rcalme/puzzle-box/Drawers/Center/center_drawer.pdf

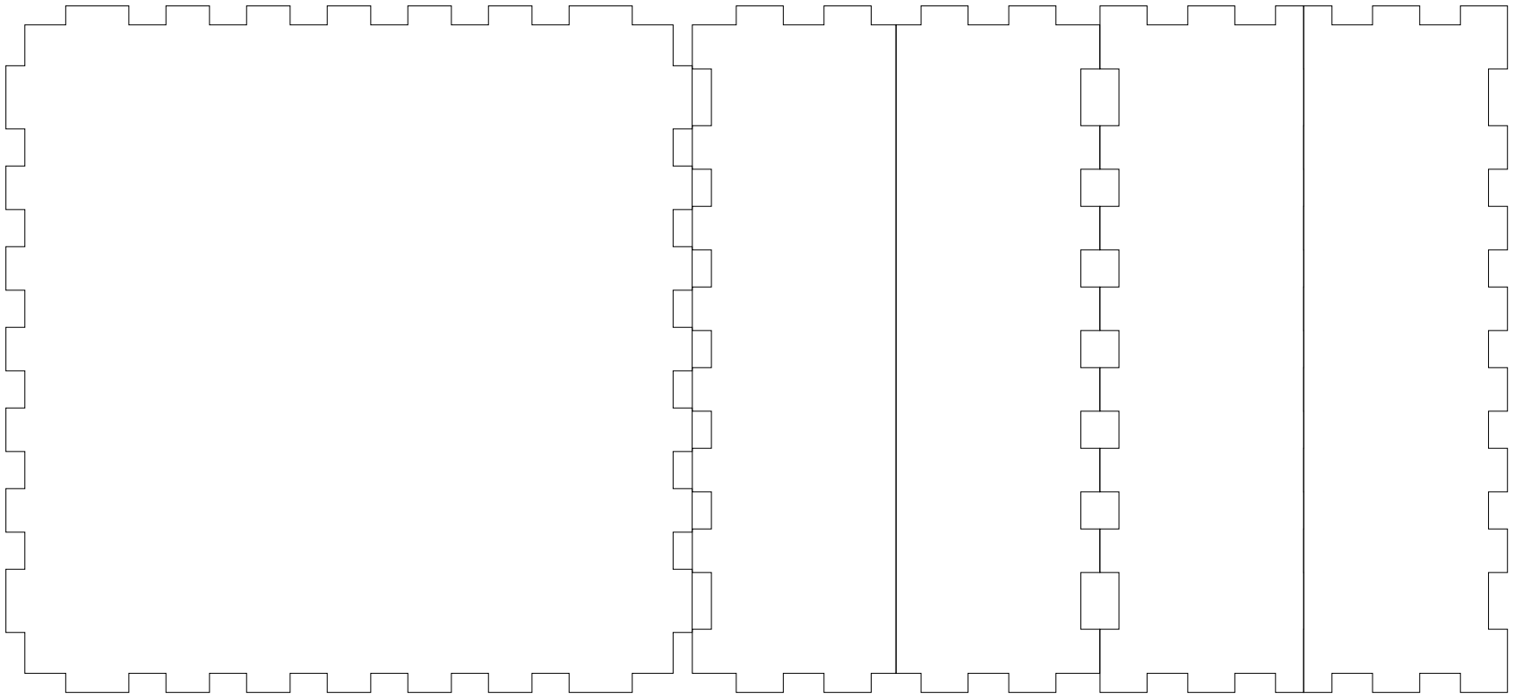
[picture p23: figure]
