rcalme/puzzle-box/Drawers/Left/left_drawer.pdf

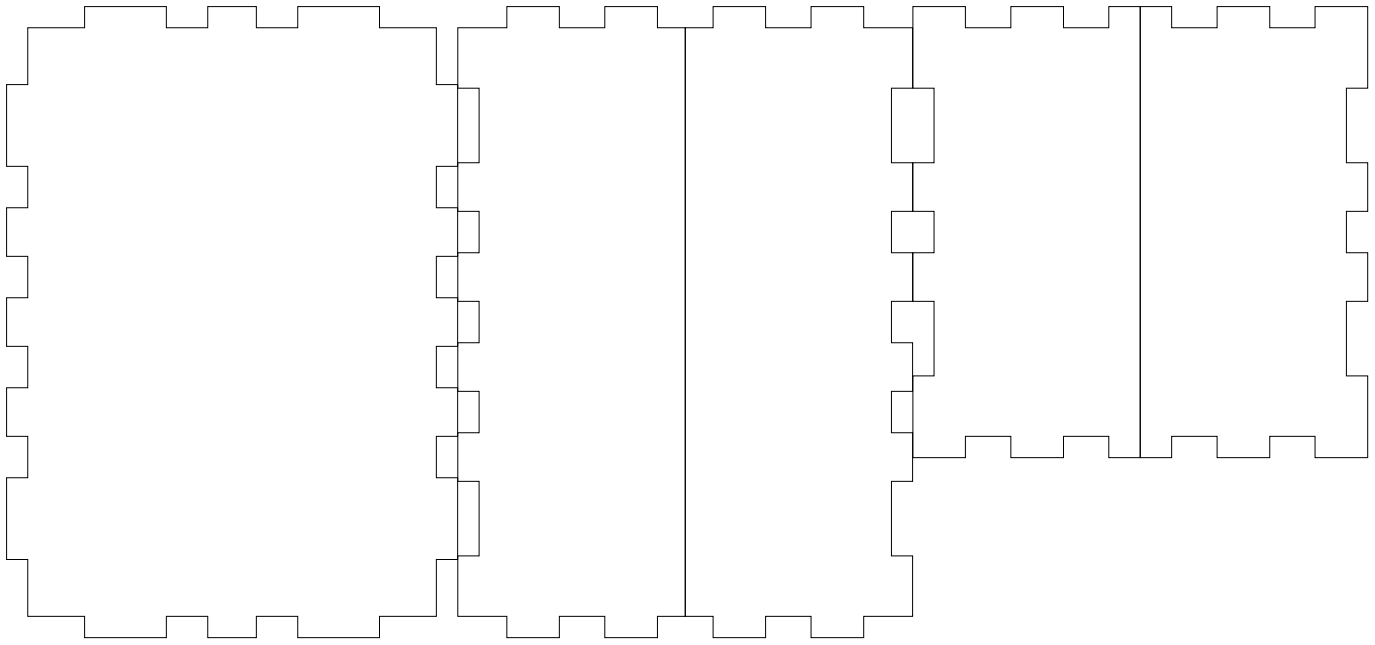
[picture p24: figure]
