rcalme/puzzle-box/All_In_One/Laser/Key_Slider/key_slider_0125_acrylic.png

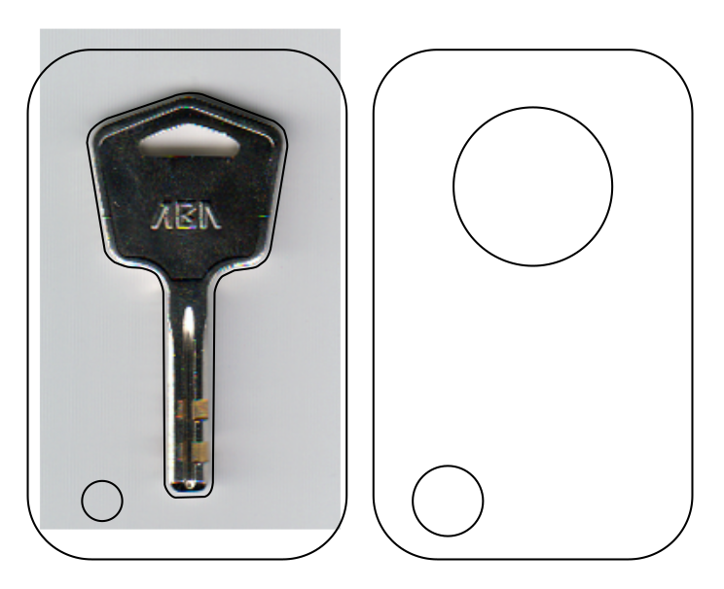
All_In_One/Laser/Key_Slider/key_slider_0125_acrylic.png
