rcalme/puzzle-box/Drawers/Key/key.png

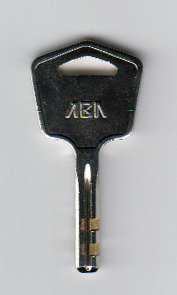
Drawers/Key/key.png
