rcalme/puzzle-box/Magnet_Grid/Clue/clue.png

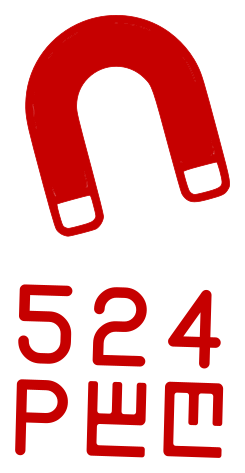
Magnet_Grid/Clue/clue.png
