rcalme/puzzle-box/Process/Images/01_Generating_gears.png

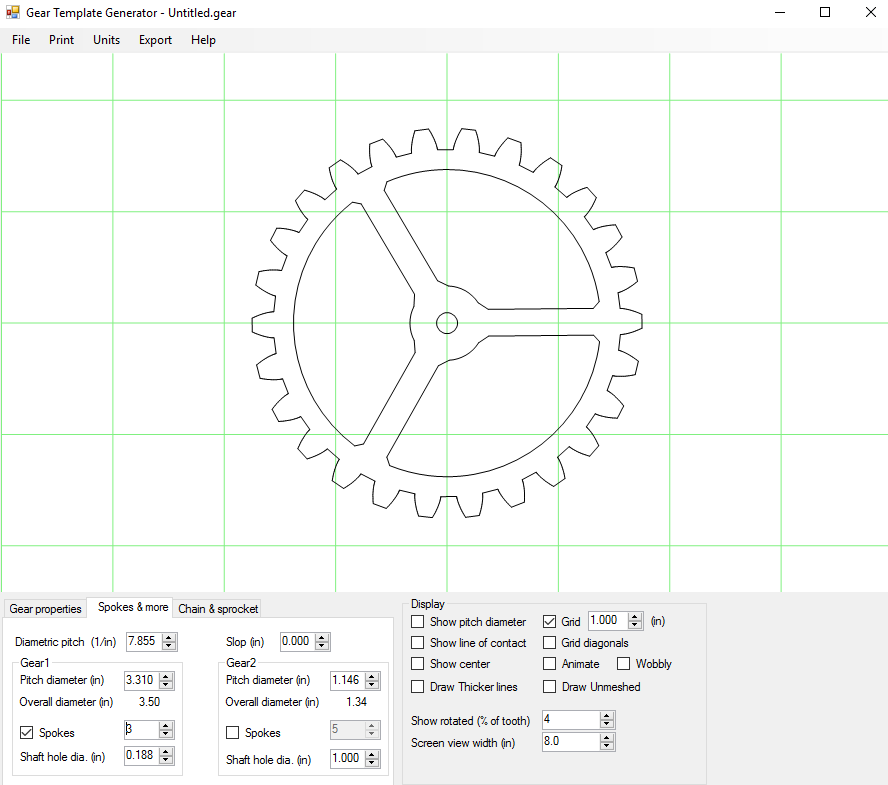
Process/Images/01_Generating_gears.png
