rcalme/puzzle-box/Process/Images/12_Peg_board_plan.png

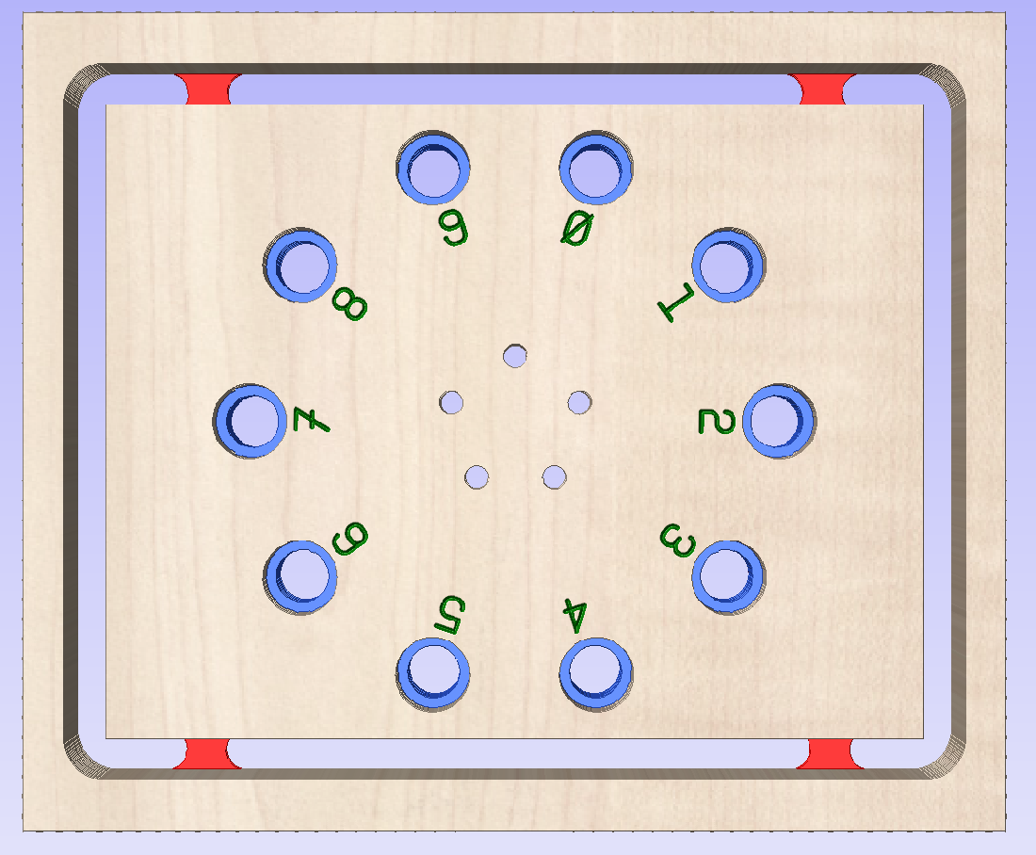
Process/Images/12_Peg_board_plan.png
