rcalme/puzzle-box/Process/Images/17_Correct_letter_settings.jpg

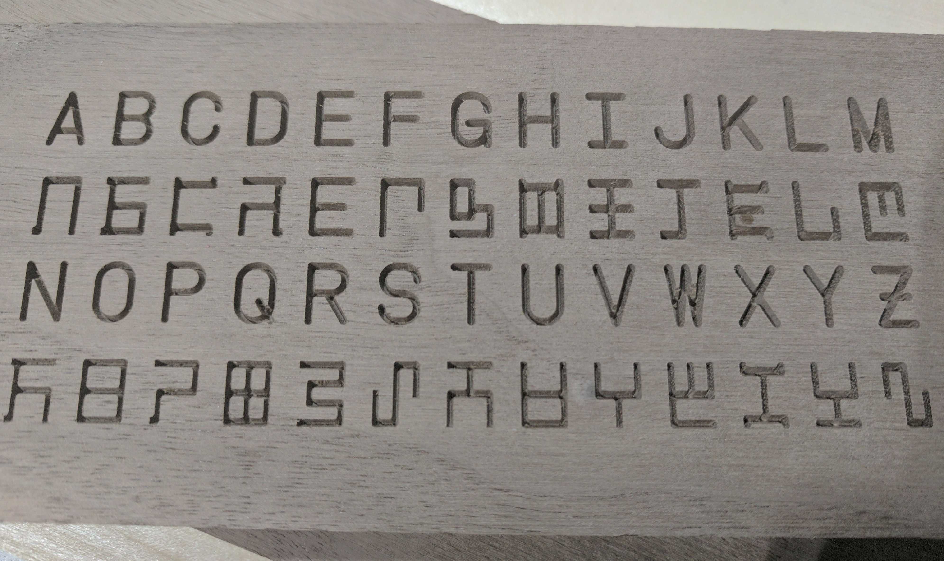
Process/Images/17_Correct_letter_settings.jpg
