rcalme/puzzle-box/Process/Images/22_Routed_feet.jpg

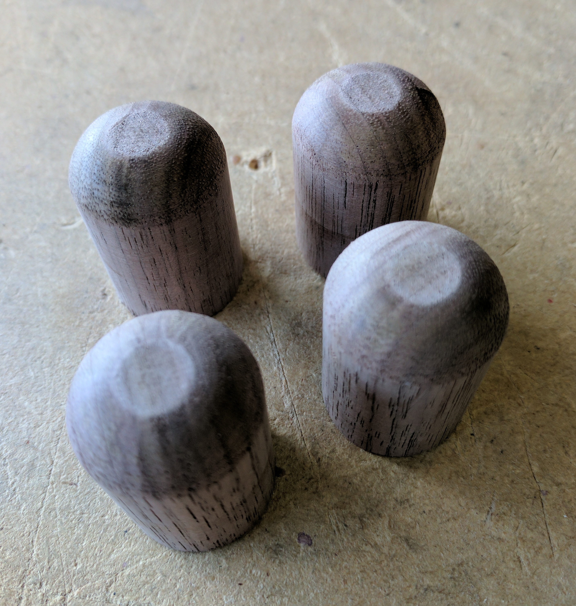
Process/Images/22_Routed_feet.jpg
