rcalme/puzzle-box/Process/Images/25_Walnut_table_saw.jpg

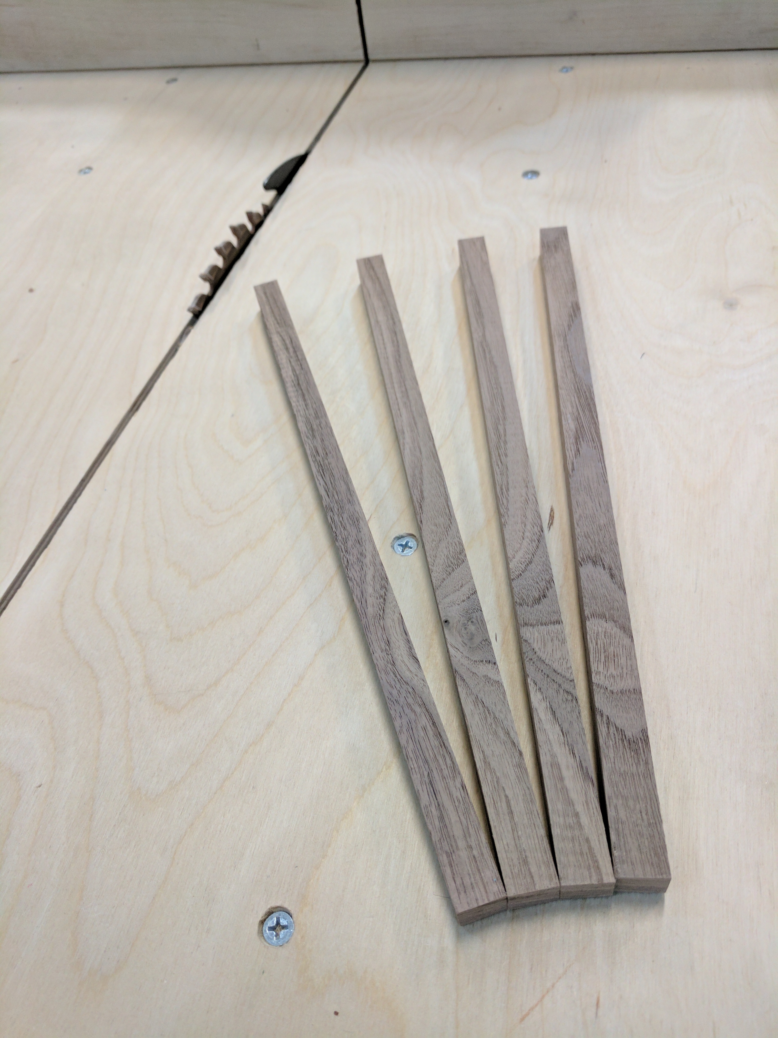
Process/Images/25_Walnut_table_saw.jpg
