rcalme/puzzle-box/Process/Images/28_Gluing_box_faces.jpg

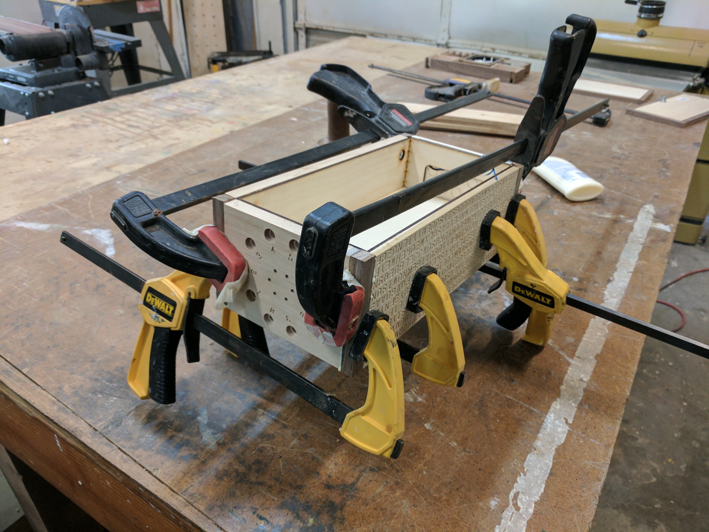
Process/Images/28_Gluing_box_faces.jpg
