rcalme/puzzle-box/Process/Images/31_Before_after_Finish.jpg

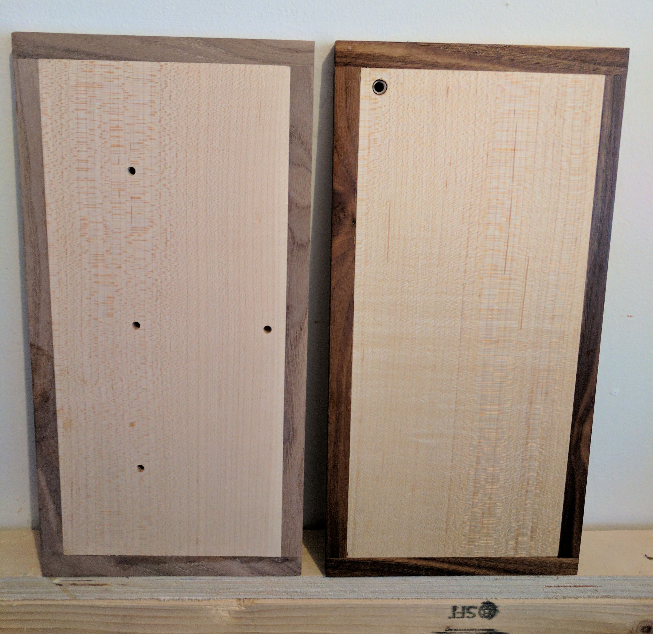
Process/Images/31_Before_after_Finish.jpg
