rcalme/puzzle-box/Process/Images/36_Box_left.jpg

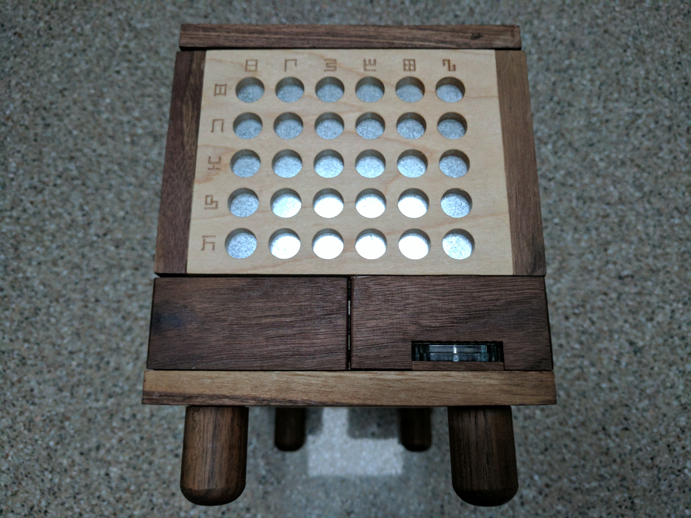
Process/Images/36_Box_left.jpg
