rcalme/puzzle-box/Rendering/3D_rendering.png

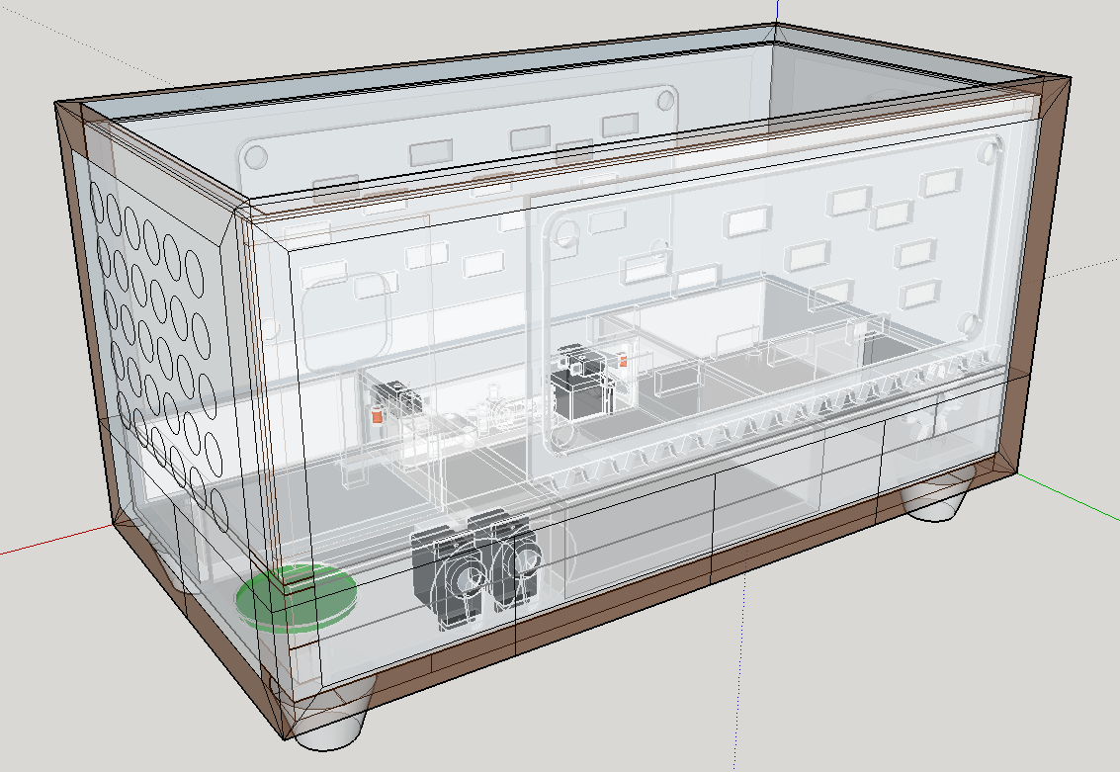
Rendering/3D_rendering.png
