rcalme/puzzle-box/Letter_Panel/Inner/latch_test.dxf

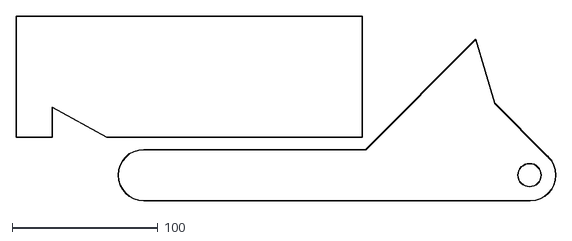
[picture p52: CAD file, 2017-05-31]
Letter_Panel/Inner/latch_test.dxf
370.0 x 126.3
