rcalme/puzzle-box/Letter_Panel/Mask/letter_mask.dxf

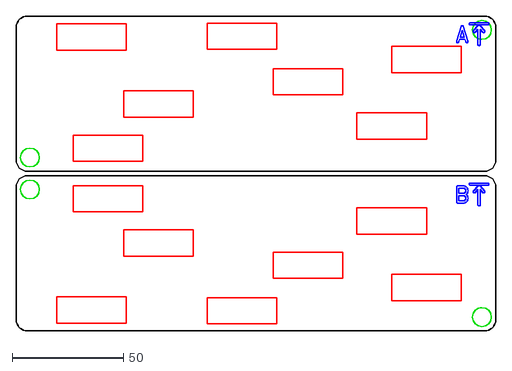
[picture p53: CAD file, 2017-06-06]
Letter_Panel/Mask/letter_mask.dxf
215.9 x 141.7
