rcalme/puzzle-box/Magnet_Grid/Internal/wire_route.dxf

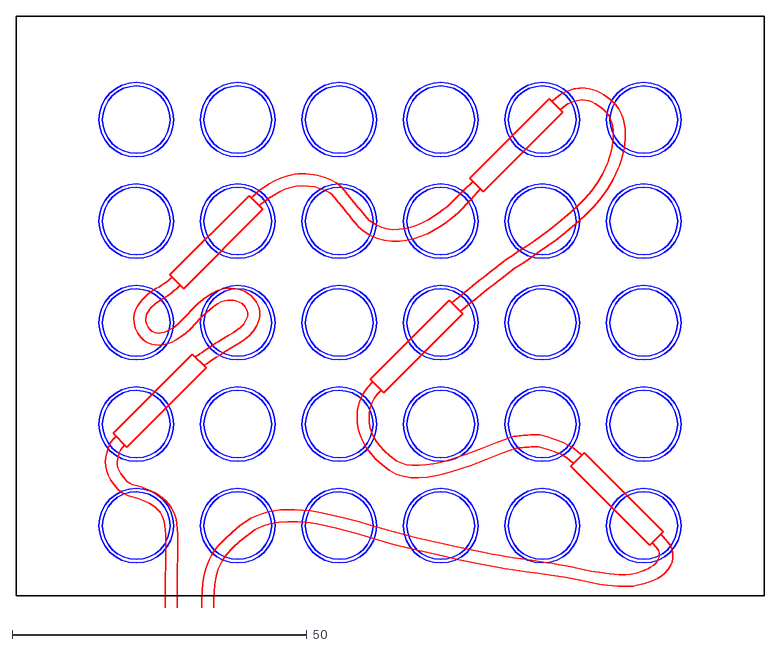
[picture p54: CAD file, 2017-03-02]
Magnet_Grid/Internal/wire_route.dxf
127.0 x 100.4
