rcalme/puzzle-box/Peg_Board/peg_board.dxf

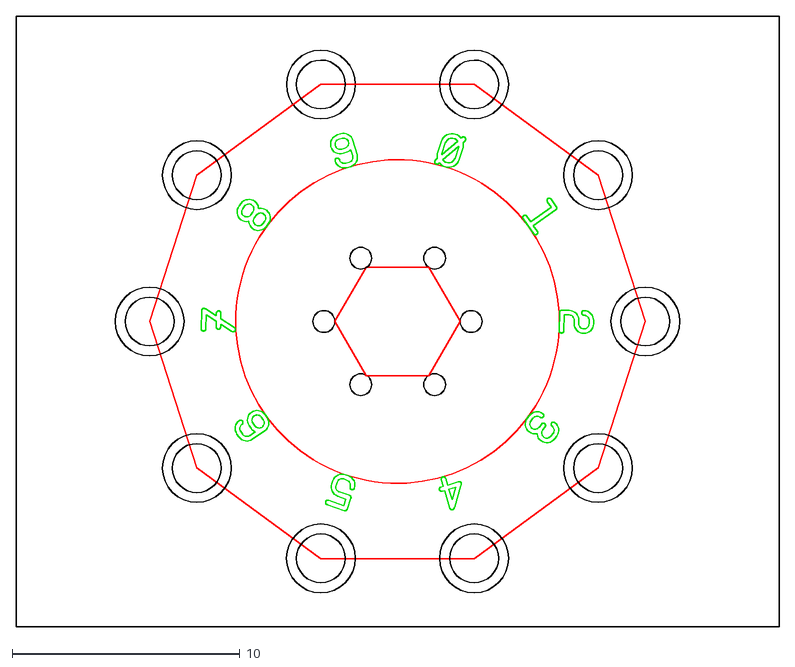
[picture p55: CAD file, 2017-06-01]
Peg_Board/peg_board.dxf
33.5 x 26.8
