rcalme/puzzle-box/Drawers/Center/guide.stl

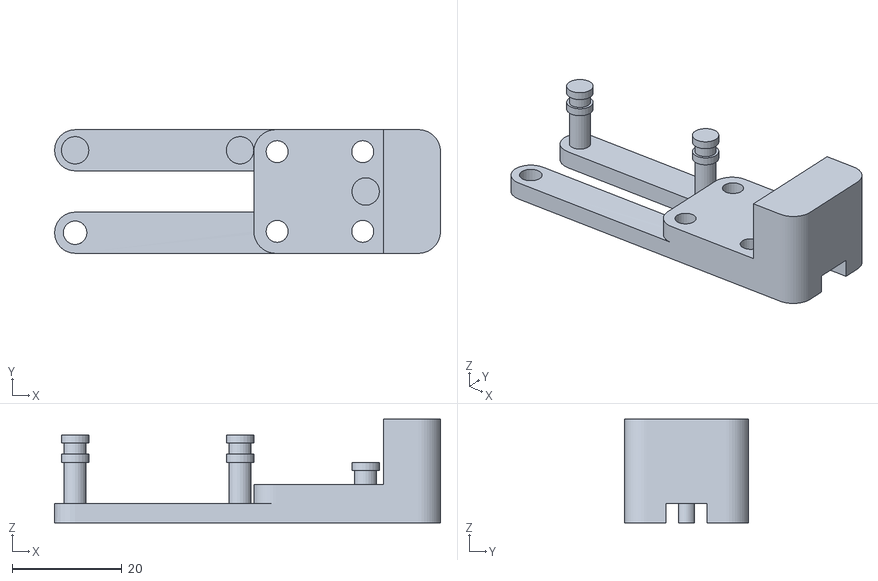
[picture p56: CAD file, 2018-02-20]
Drawers/Center/guide.stl
70.2 x 22.5 x 18.9
