rcalme/puzzle-box/Drawers/Key/key.dxf

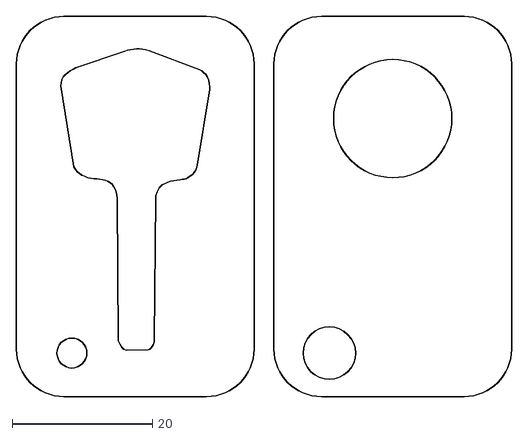
[picture p57: CAD file, 2017-06-09]
Drawers/Key/key.dxf
70.6 x 54.2
