rcalme/puzzle-box/Drawers/Right/right_drawer.dxf

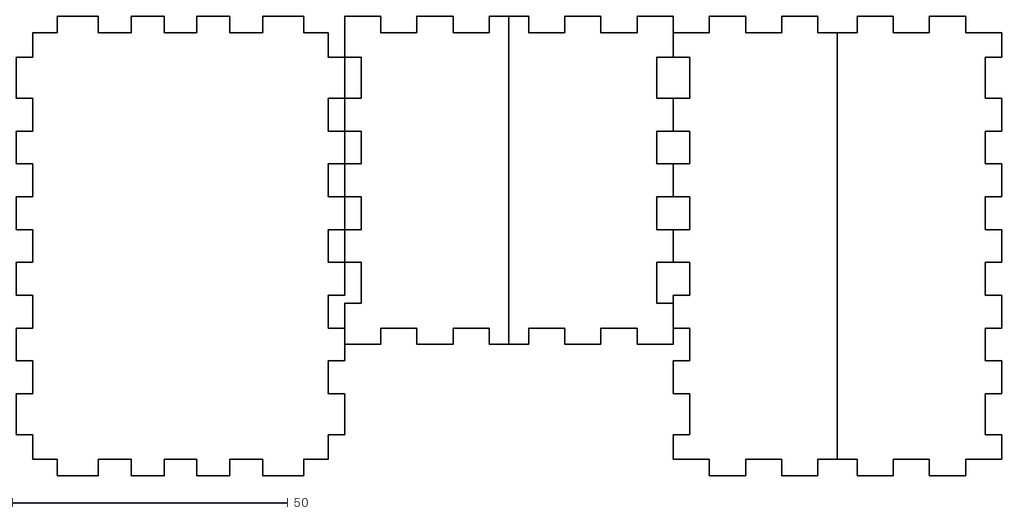
[picture p58: CAD file, 2017-02-18]
Drawers/Right/right_drawer.dxf
178.7 x 83.3
