rcalme/puzzle-box/Letter_Panel/Inner/mask_plate.dxf

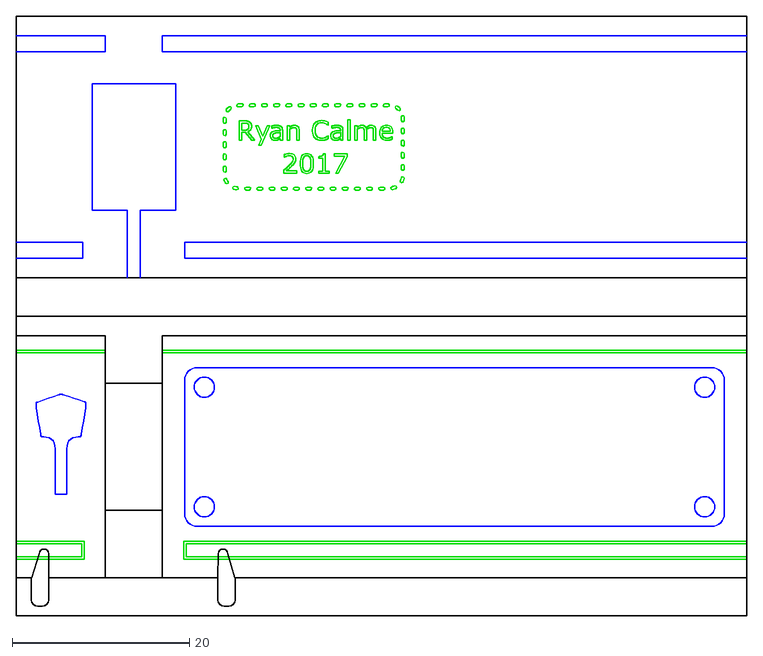
[picture p59: CAD file, 2017-03-21]
Letter_Panel/Inner/mask_plate.dxf
82.4 x 67.7
