rcalme/puzzle-box/Peg_Board/peg_board_middle_layer.dxf

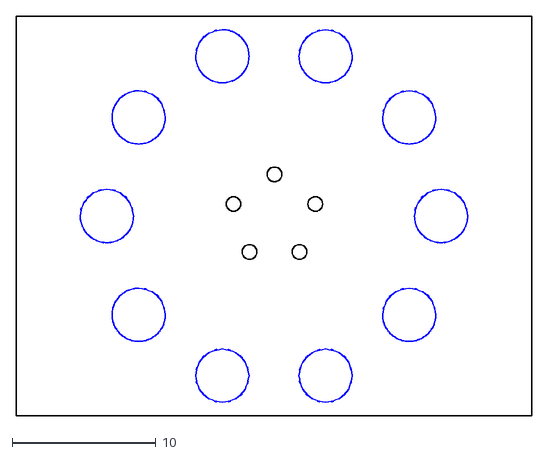
[picture p60: CAD file, 2017-03-21]
Peg_Board/peg_board_middle_layer.dxf
35.8 x 27.8
