rcalme/puzzle-box/Drawers/Center/slider.stl

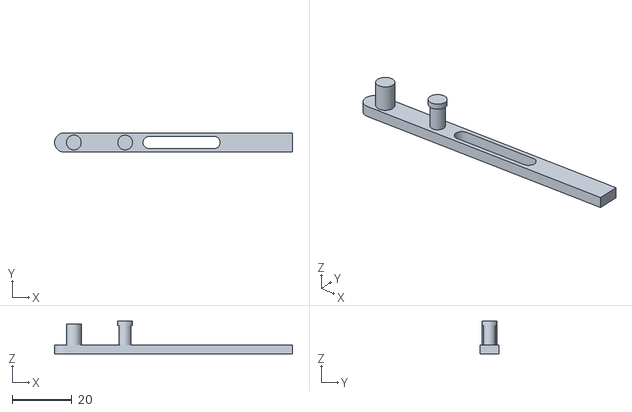
[picture p61: CAD file, 2018-02-20]
Drawers/Center/slider.stl
80.0 x 6.50 x 11.0
