rcalme/puzzle-box/Drawers/Key/servo_bracket.stl

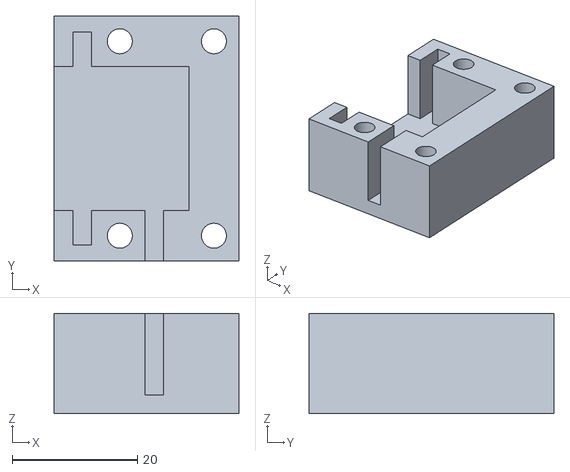
[picture p62: CAD file, 2017-06-09]
Drawers/Key/servo_bracket.stl
29.5 x 39.0 x 16.0
