rcalme/puzzle-box/Drawers/Center/center_drawer.dxf

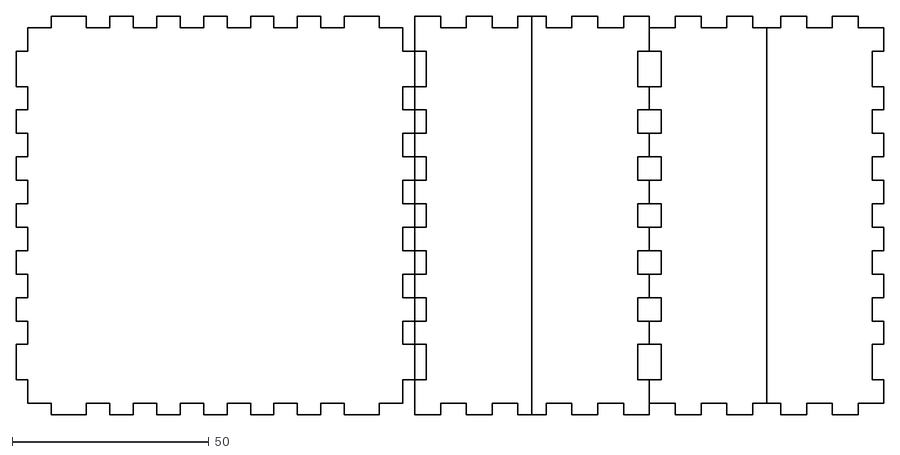
[picture p63: CAD file, 2017-02-18]
Drawers/Center/center_drawer.dxf
220.3 x 101.2
