rcalme/puzzle-box/Process/Images/14_Test_lettering.jpg

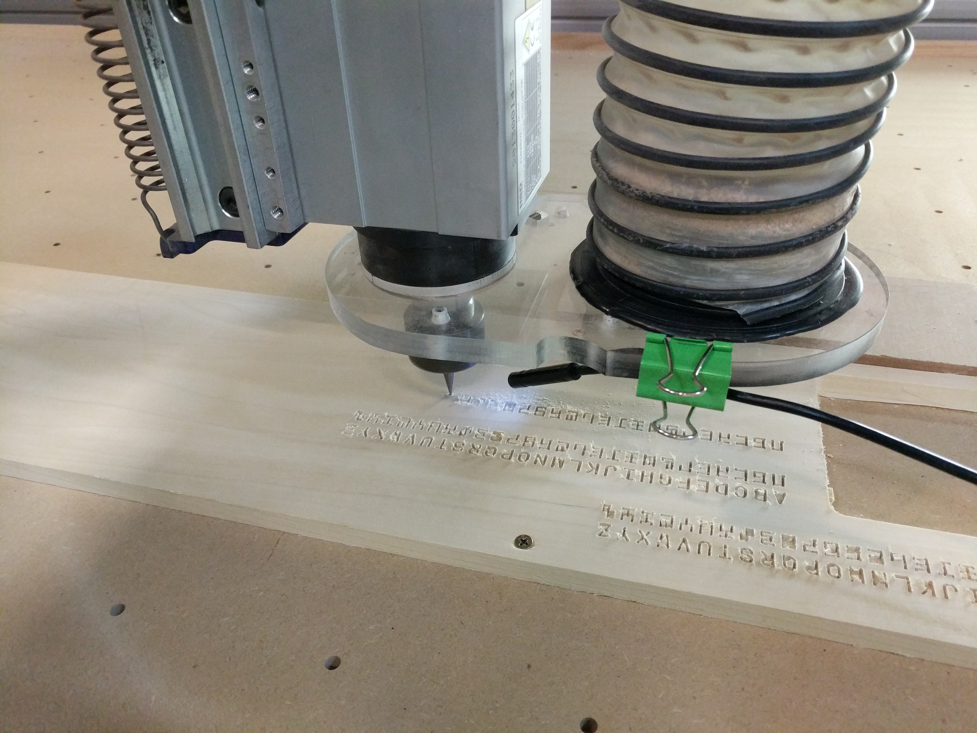
Process/Images/14_Test_lettering.jpg
