rcalme/puzzle-box/Cipher_Gears/Individual_Gears/5_spoke_3.5_inch.pdf

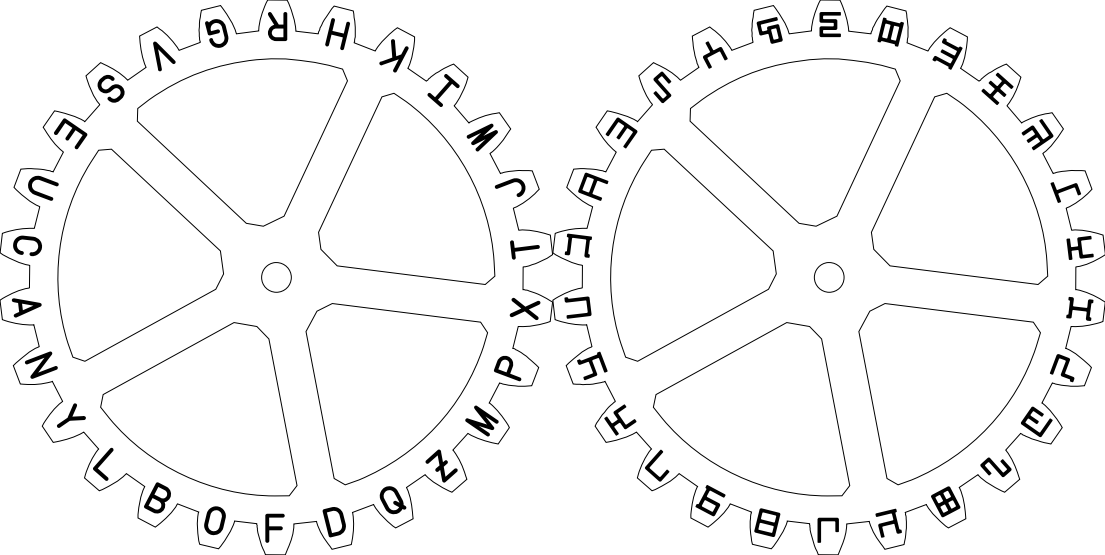
[picture p82: page 1]
