rcalme/puzzle-box/Cipher_Gears/Individual_Gears/6_spoke_3.5_inch.pdf

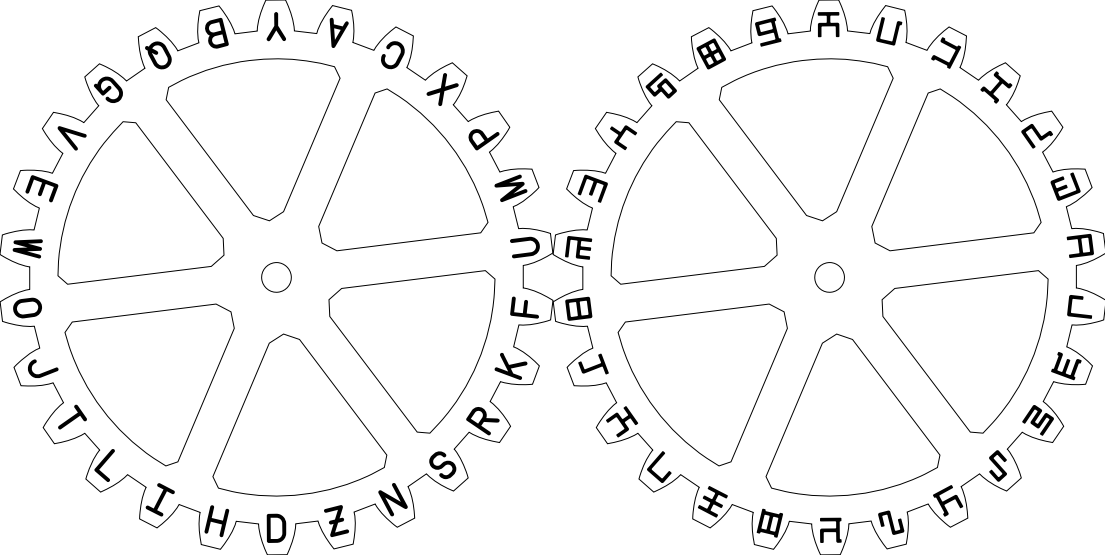
[picture p83: page 1]
