rcalme/puzzle-box/Cipher_Gears/Foam_Cutout/gear_cutout.pdf

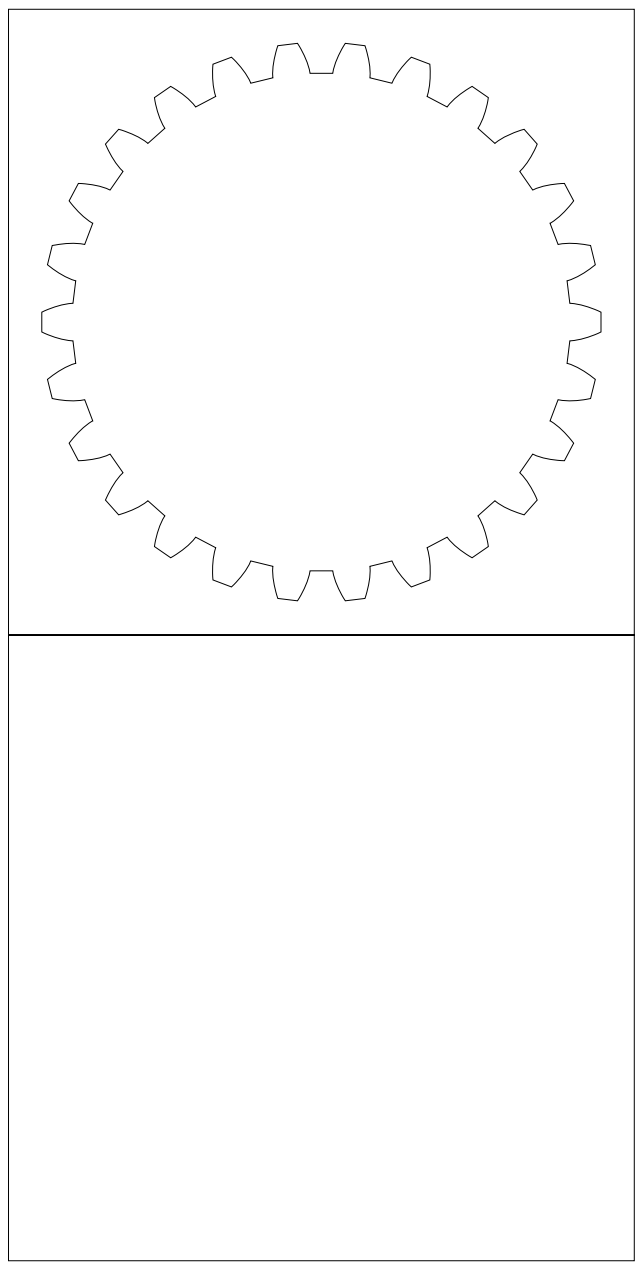
[picture p84: page 1]
